mistic100/Nixie-Clock-IN2/firmware/src/ZigbeeController.hpp

#pragma once

#include <Arduino.h>
#include <Zigbee.h>
#include "constants.hpp"
#include "CustomZigbeeEP.hpp"
#include "Settings.hpp"

#define TAG_ZB "ZB"

typedef enum
{
    CLICK = 0,
    DOUBLE_CLICK = 1,
    LONG_CLICK = 2,
} btn_action_t;

class ZigbeeController
{
private:
    ZigbeeLight _mainSwitch = ZigbeeLight(ZIGBEE_ENDPOINT_MAIN);
    ZigbeeTempSensor _tempSensor = ZigbeeTempSensor(ZIGBEE_ENDPOINT_BME280);
    ZigbeeColorDimmableLight _leds = ZigbeeColorDimmableLight(ZIGBEE_ENDPOINT_LEDS);
    CustomZigbeeEP _customEp = CustomZigbeeEP(ZIGBEE_ENDPOINT_CUSTOM);

public:
    void begin()
    {
        _mainSwitch.setManufacturerAndModel(ZIGBEE_MANUFACTURER, ZIGBEE_MODEL);
        _mainSwitch.addTimeCluster();

        _tempSensor.setMinMaxValue(-40, 85);
        _tempSensor.setTolerance(0.1);
        _tempSensor.addHumiditySensor(0, 100, 0.1);

        _leds.setLightColorCapabilities(ZIGBEE_COLOR_CAPABILITY_HUE_SATURATION);

        Zigbee.addEndpoint(&_mainSwitch);
        Zigbee.addEndpoint(&_tempSensor);
        Zigbee.addEndpoint(&_leds);
        Zigbee.addEndpoint(&_customEp);

        if (!Zigbee.begin())
        {
            ESP_LOGE(TAG_ZB, "Zigbee failed to start");
            delay(1000);
            esp_restart();
        }
        else
        {
            ESP_LOGI(TAG_ZB, "Zigbee started successfully");
        }

        ESP_LOGI(TAG_ZB, "Connecting to network");
        while (!Zigbee.connected())
        {
            Serial.print(".");
            delay(100);
        }
        Serial.println();

        ESP_LOGI(TAG_ZB, "Ready");

        _mainSwitch.setLight(settings.getState());

        _tempSensor.setReporting(1, 0, 0.1);
        _tempSensor.setHumidityReporting(1, 0, 0.1);

        _leds.setLightState(true);
        _leds.setLightColor(settings.getLedColor());

        _customEp.setTempOffset(settings.getTempOffset() * 100);
    }

    void loop()
    {
        _customEp.loop();
    }

    void toggleMainSwitch()
    {
        _mainSwitch.setLight(!_mainSwitch.getLightState());
    }

    void onMainSwitchChange(void (*callback)(bool))
    {
        _mainSwitch.onLightChange(callback);
    }

    void onLedColorChange(ZigbeeColorLightHsvCallback callback)
    {
        _leds.onLightChangeHsv(callback);
    }

    void onWeather(void (*callback)(uint8_t))
    {
        _customEp.onWeather(callback);
    }

    void onTempOffset(void (*callback)(int16_t))
    {
        _customEp.onTempOffset(callback);
    }

    void sendBtnEvent(u8_t button_id, btn_action_t action)
    {
        _customEp.sendEvent(button_id, action);
    }

    void setTempAndHumidity(float temp, float humi)
    {
        _tempSensor.setTemperature(temp);
        _tempSensor.setHumidity(humi);
    }

    void requestTime()
    {
        ESP_LOGI(TAG_ZB, "Request time");
        tm timeinfo = _mainSwitch.getTime();
        timeKeeper.setTime(timeinfo);
    }
};

ZigbeeController zigbeeCtrl;
